aravind7s/ADP2384_EVL/Simulation_Files/ADP2384.asc

C1: cap; 22n
C2: cap; 0.1µ; V=16 Irms=0 Rser=0.2 Lser=0
C3: cap; 47µ; V=10
C4: cap; 1500p; V=50 Irms=0 Rser=0 Lser=0
C5: cap; 1µ; V=16
C6: cap; 4.7p; V=50
C7: cap; 10µ; V=25
C8: cap; 47µ; V=10
C9: cap; 10µ; V=25
L1: ind; 3.3µ; Ipk=18.6 Rser=0.0108 Rpar=0 Cpar=0 mfg="Vishay" pn="IHLP4040DZ01-3R3"
R1: res; 10K; tol=1 pwr=0.125
R2: res; 2.21k; tol=1 pwr=0.125
R3: res; 100k; tol=1 pwr=0.125
R4: res; 31.6k; tol=1 pwr=0.125
R5: res; 100K
Rload: res; 825m
U1: ADP2384
V1: voltage; 12
Named nets: 0, OUT, IN
.tran 6m startup
